alperyazar/aPCmeter/Board/aPCmeter_sch_bb.png

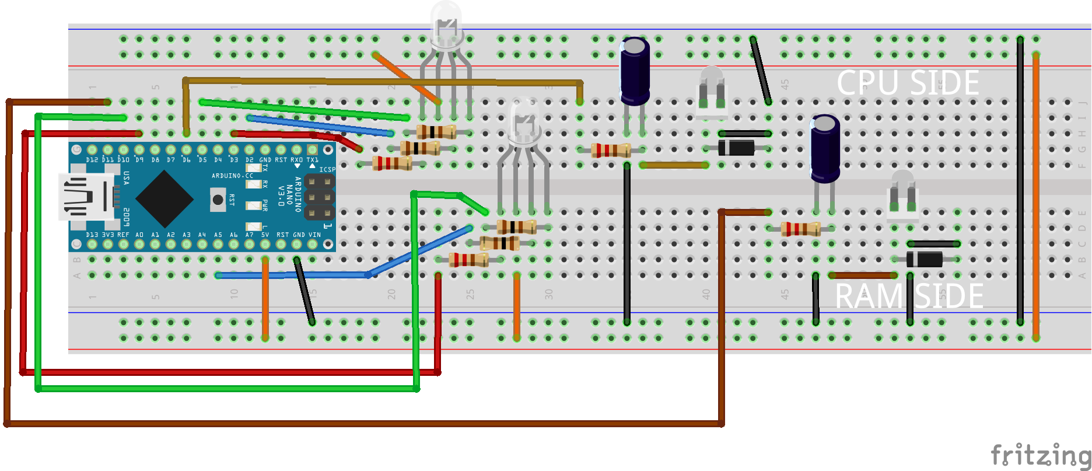
Board/aPCmeter_sch_bb.png
