alperyazar/aPCmeter/Firmware/doxygen/images/aPCmeter_2.jpg

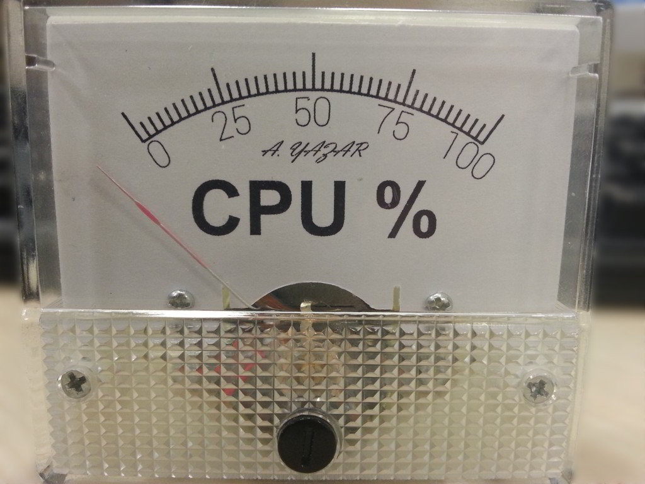
Firmware/doxygen/images/aPCmeter_2.jpg
