alperyazar/aPCmeter/Firmware/doxygen/images/aPCmeter_6.jpg

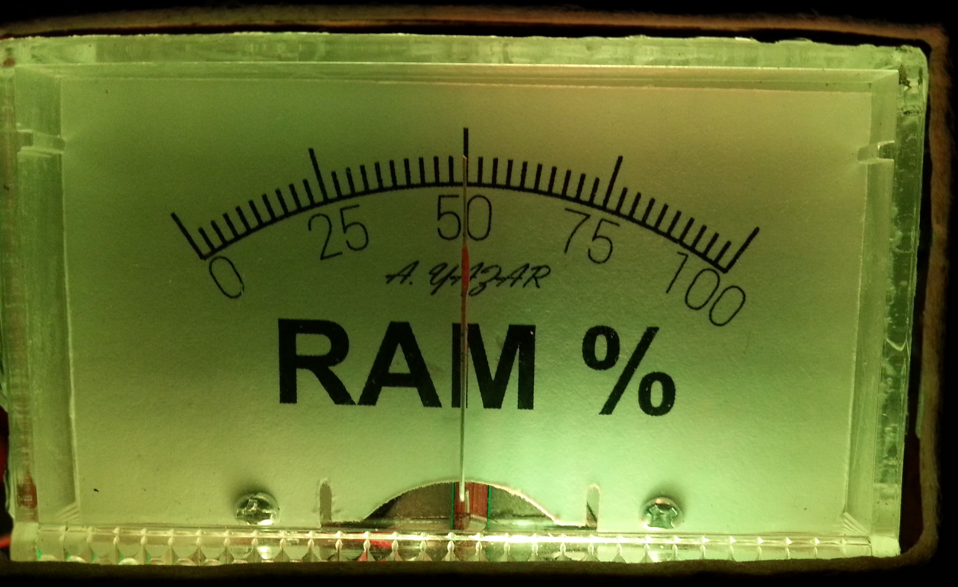
Firmware/doxygen/images/aPCmeter_6.jpg
