alperyazar/aPCmeter/Firmware/doxygen/images/aPCmeter_white_annotated_1024_721.jpg

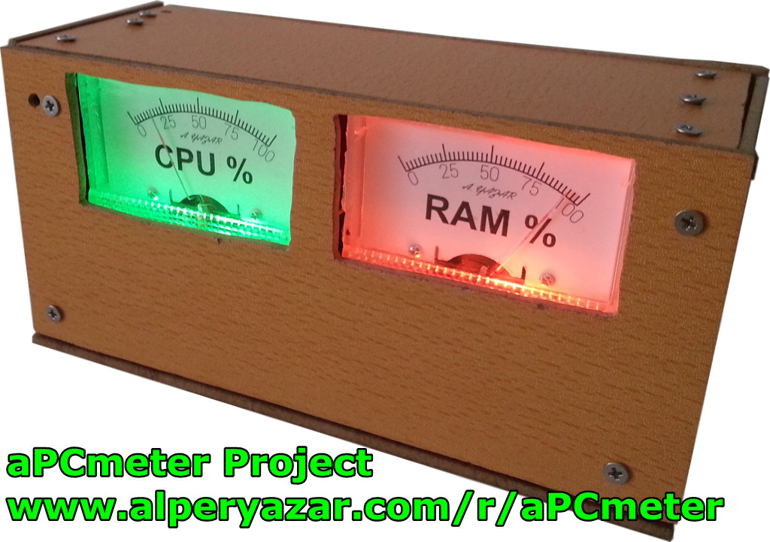
Firmware/doxygen/images/aPCmeter_white_annotated_1024_721.jpg
