alperyazar/aPCmeter/Gauge/gauge_cpu.png

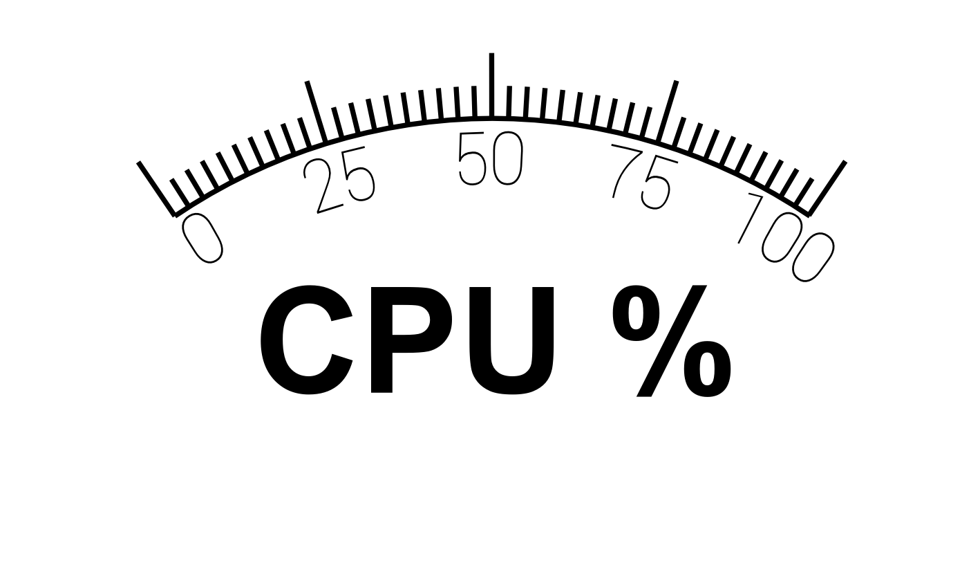
Gauge/gauge_cpu.png
