alperyazar/aPCmeter/Gauge/gauge_cpu_ayazar.png

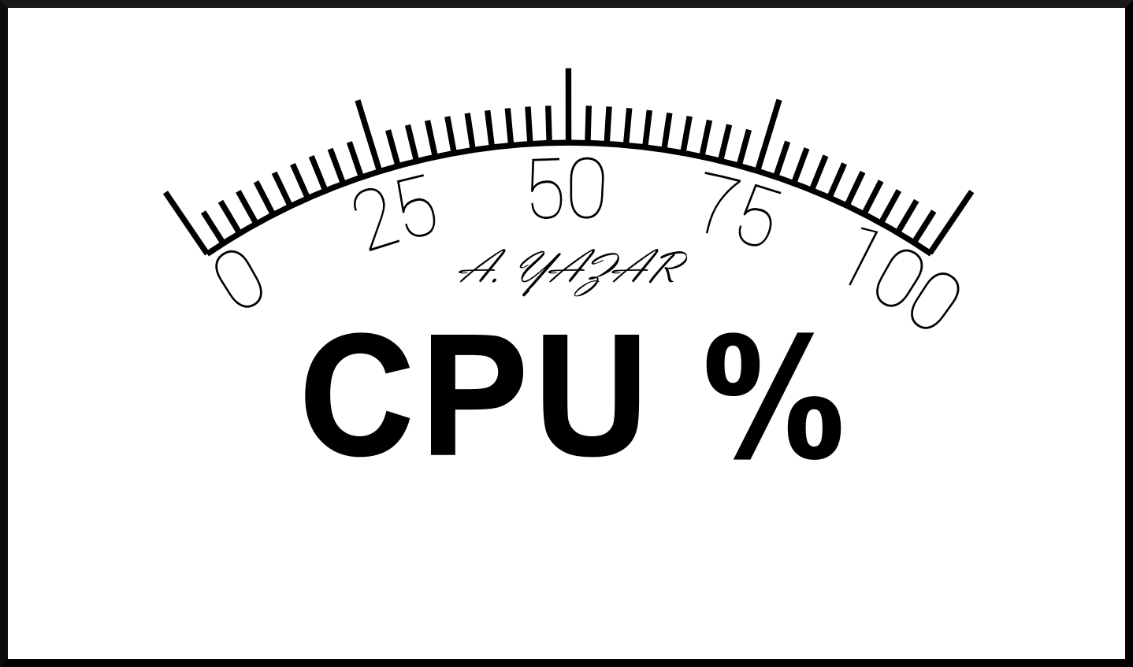
Gauge/gauge_cpu_ayazar.png
